FITLab-Swansea/ageing-well-toolkit/3D_Models/DoorLever2.stl

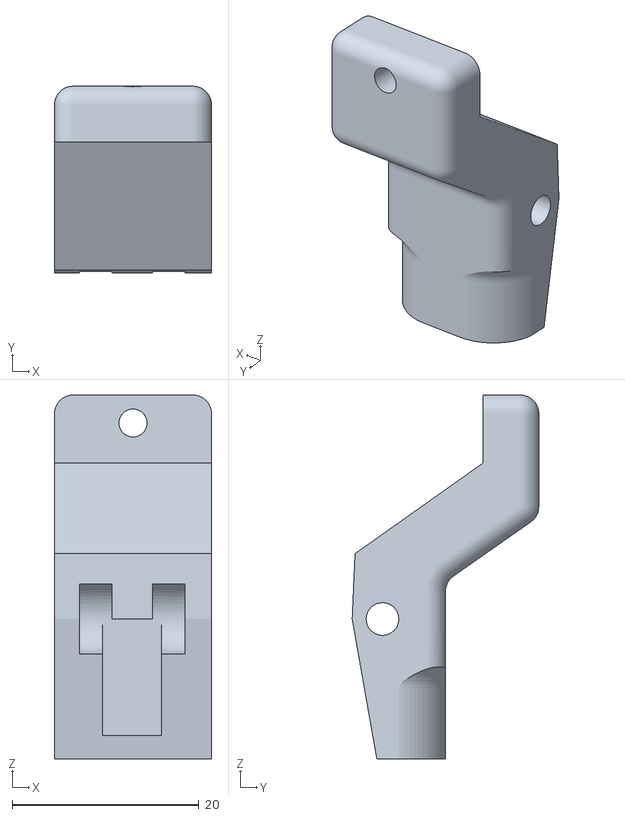
[picture p24: CAD file, 2024-07-04]
3D_Models/DoorLever2.stl
16.8 x 20.0 x 39.0
