FITLab-Swansea/ageing-well-toolkit/3D_Models/Pod.stl

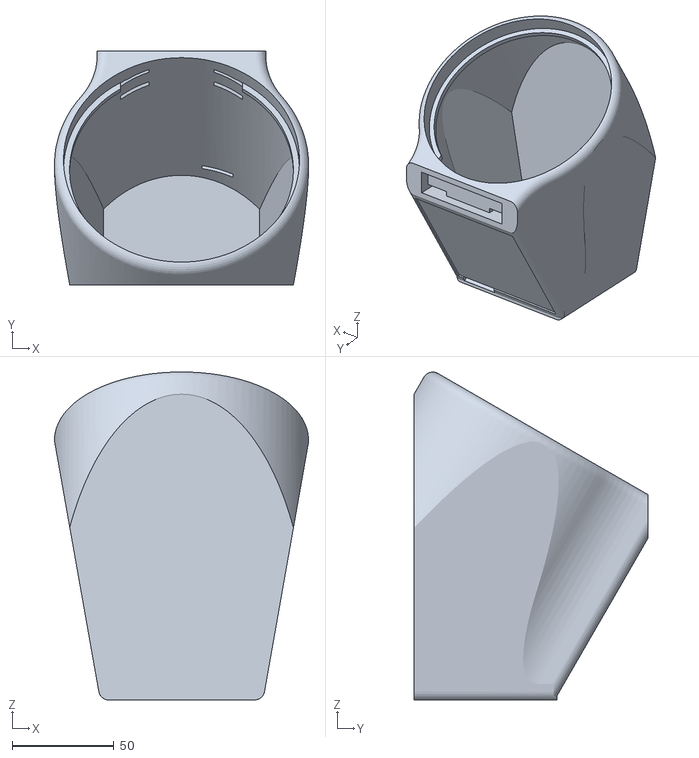
[picture p25: CAD file, 2024-07-04]
3D_Models/Pod.stl
125.0 x 115.0 x 161.2
